SidSam15/The-Operator/Media Assets/image-3.png

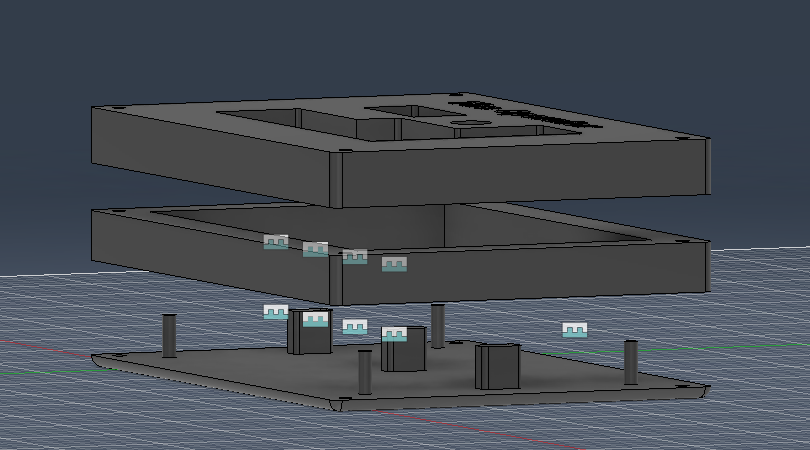
Media Assets/image-3.png
